Qu3d45/Dissertacao_final/Apendice/Diagrama_Blocos.png

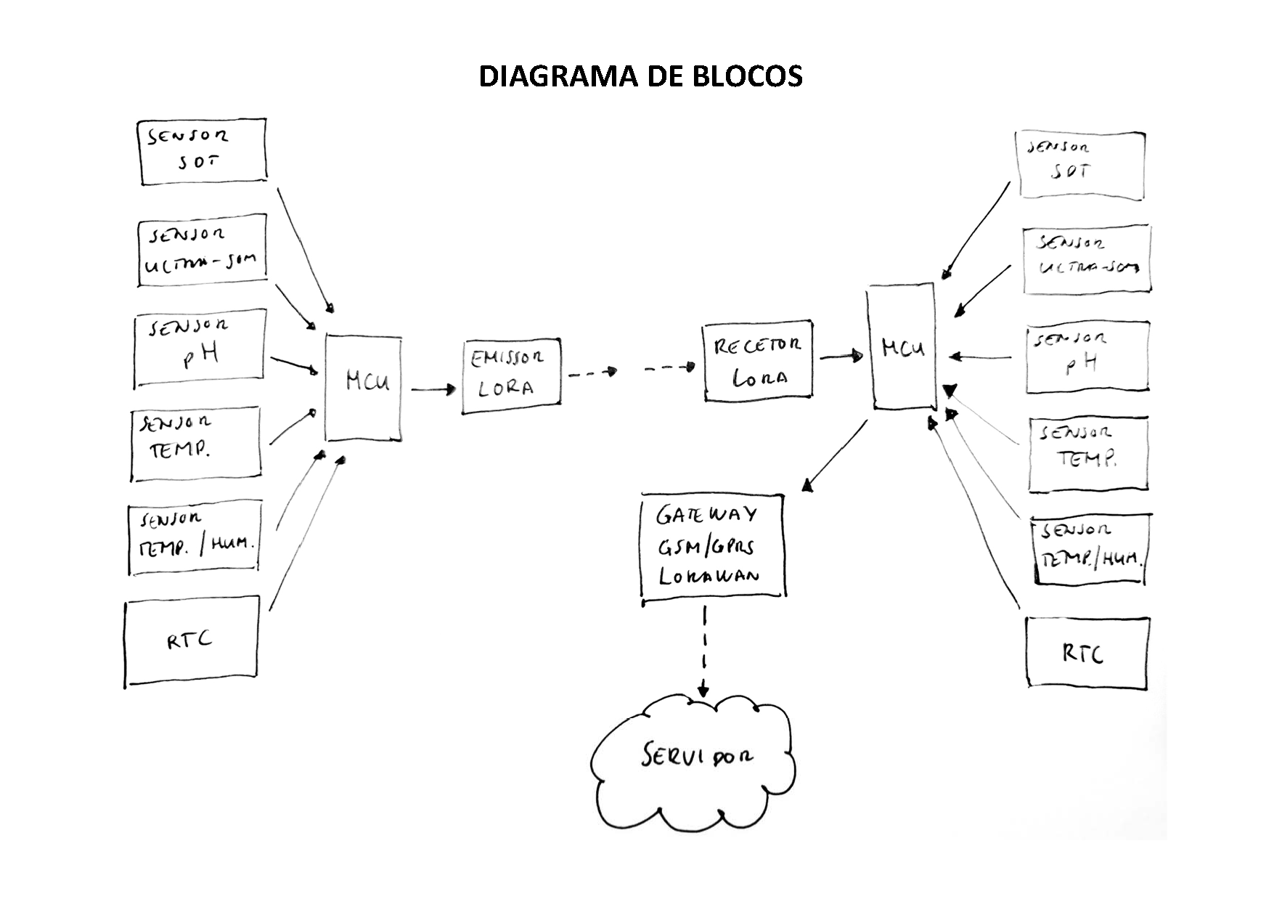
Apendice/Diagrama_Blocos.png
