Qu3d45/Dissertacao_final/Imagens_diagramas/20191011_103415.jpg

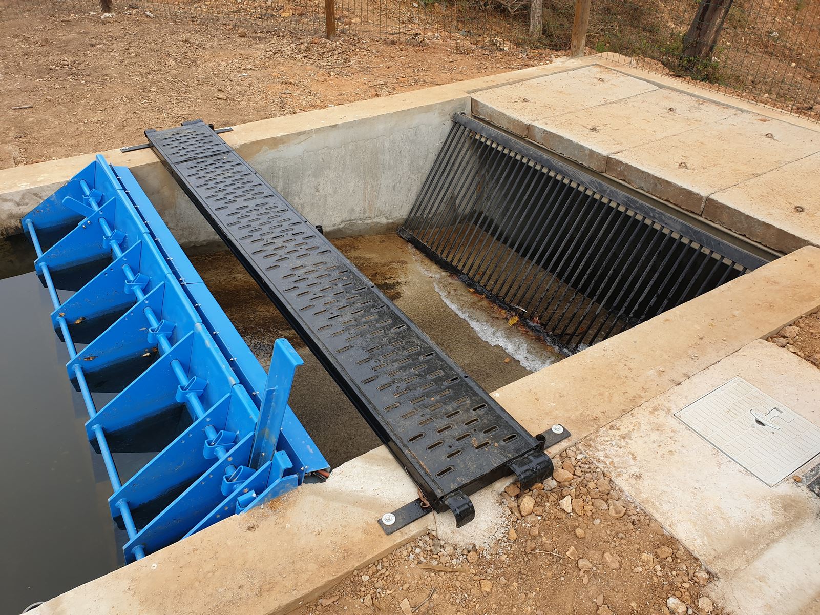
Imagens_diagramas/20191011_103415.jpg
