Qu3d45/Dissertacao_final/Imagens_diagramas/bat_liga.png

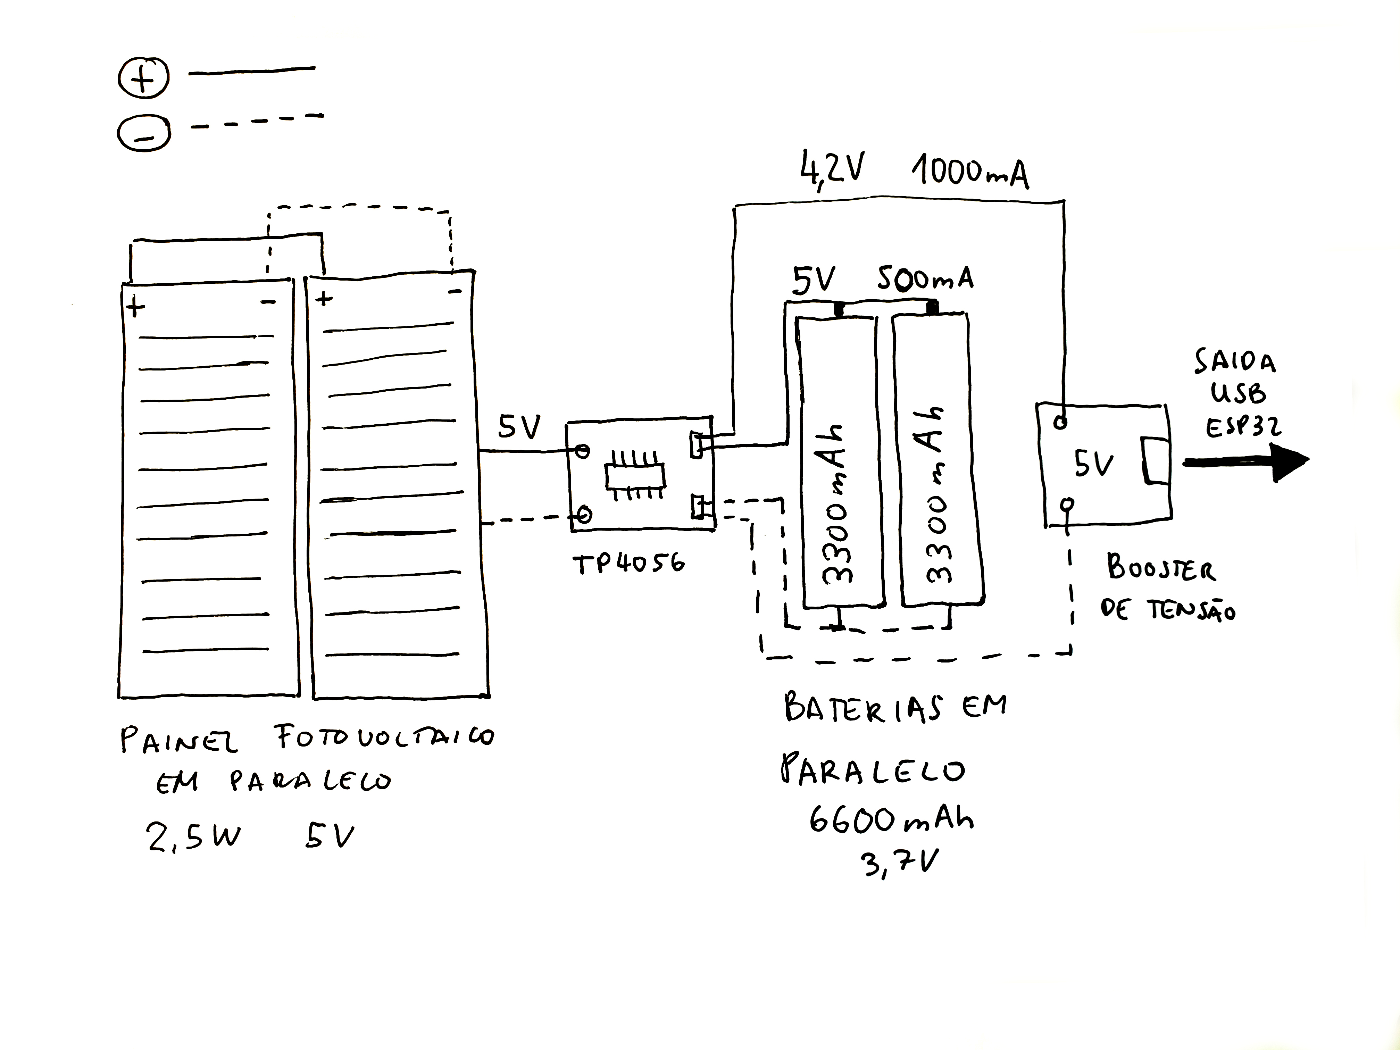
Imagens_diagramas/bat_liga.png
