Qu3d45/Dissertacao_final/Imagens_diagramas/bat_super.png

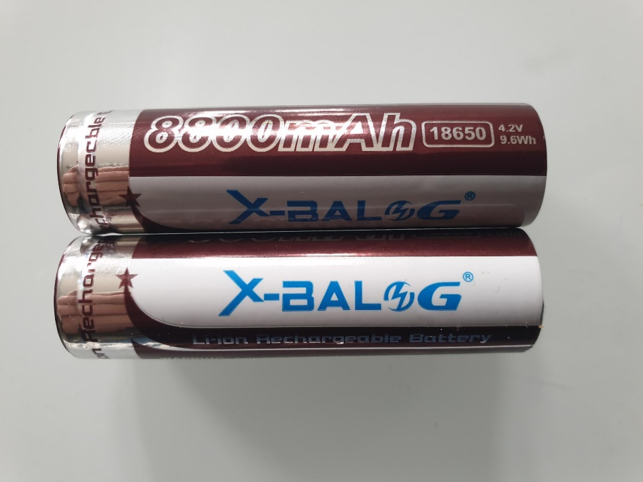
Imagens_diagramas/bat_super.png
