Qu3d45/Dissertacao_final/Imagens_diagramas/bateria.png

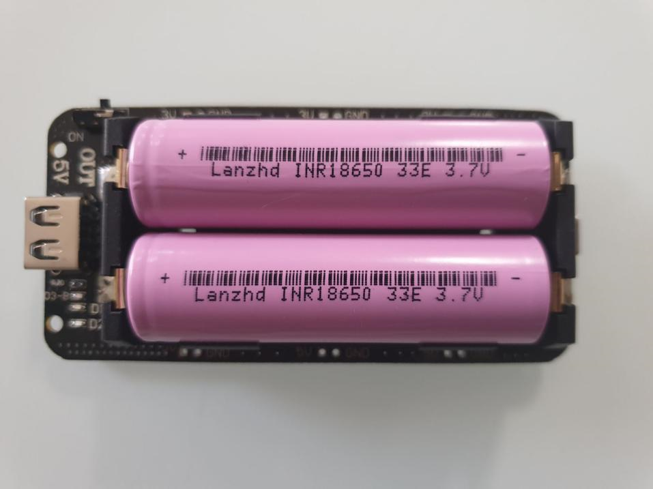
Imagens_diagramas/bateria.png
