Qu3d45/Dissertacao_final/Imagens_diagramas/bloco_emissor.png

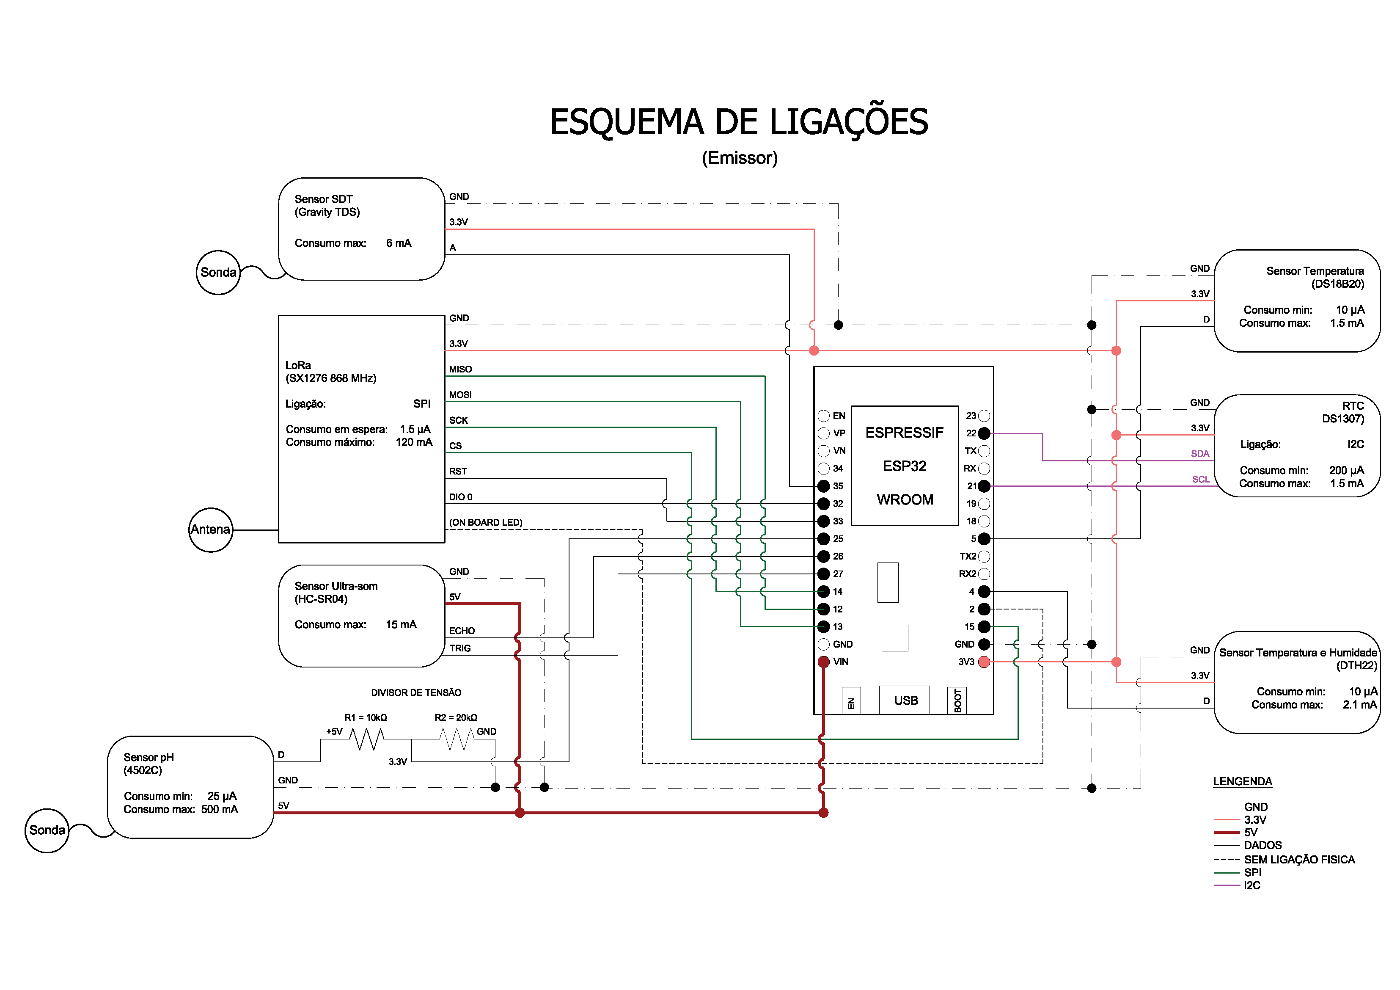
Imagens_diagramas/bloco_emissor.png
