Qu3d45/Dissertacao_final/Imagens_diagramas/bloco_gateway.png

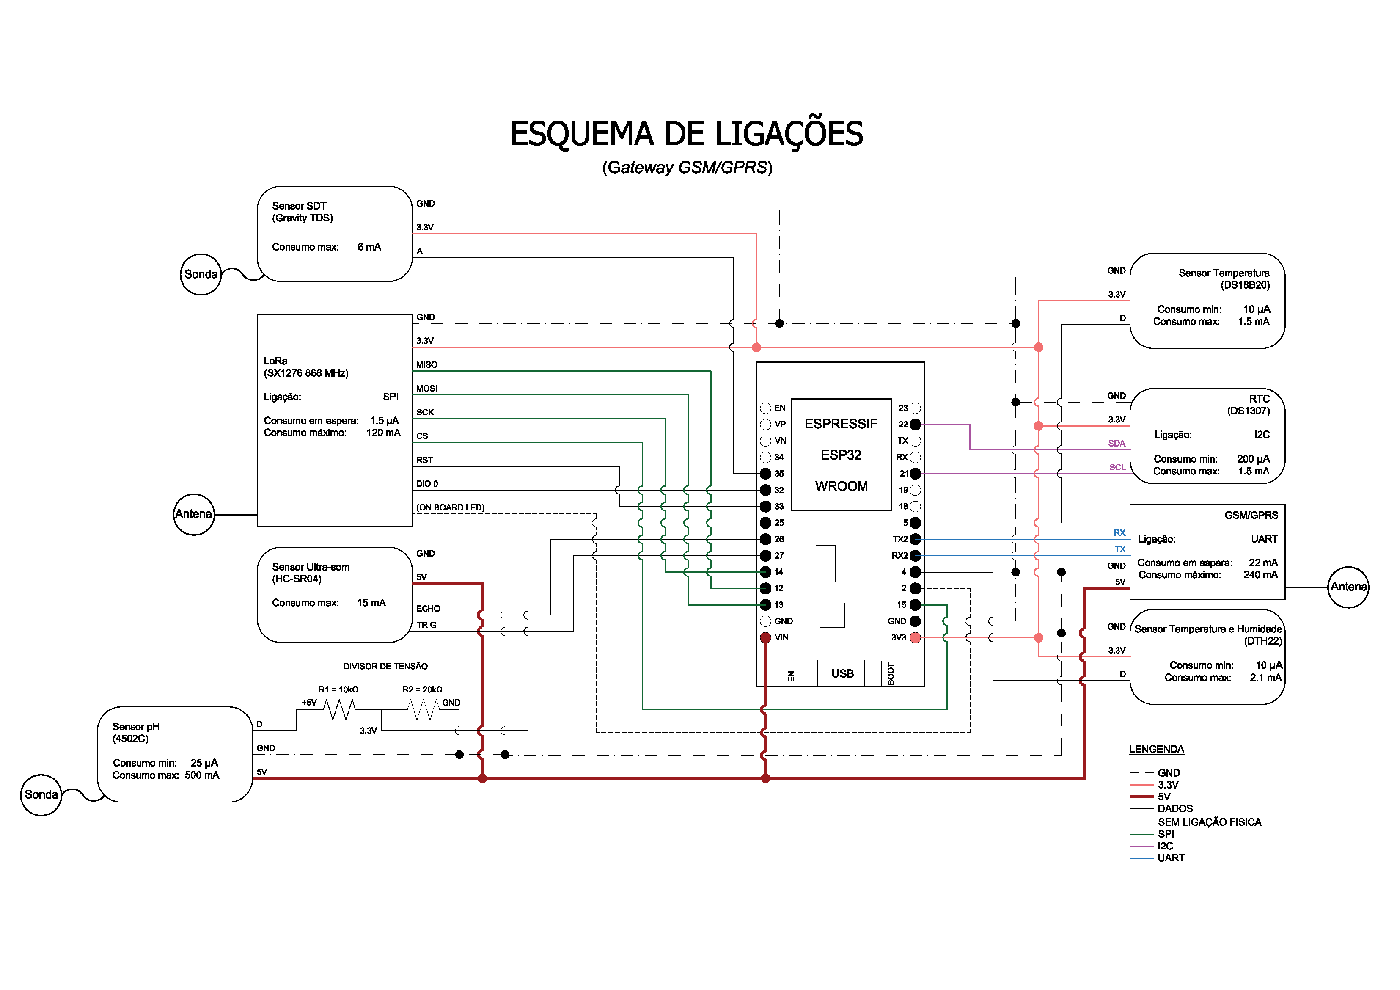
Imagens_diagramas/bloco_gateway.png
