Qu3d45/Dissertacao_final/Imagens_diagramas/caudal_1.png

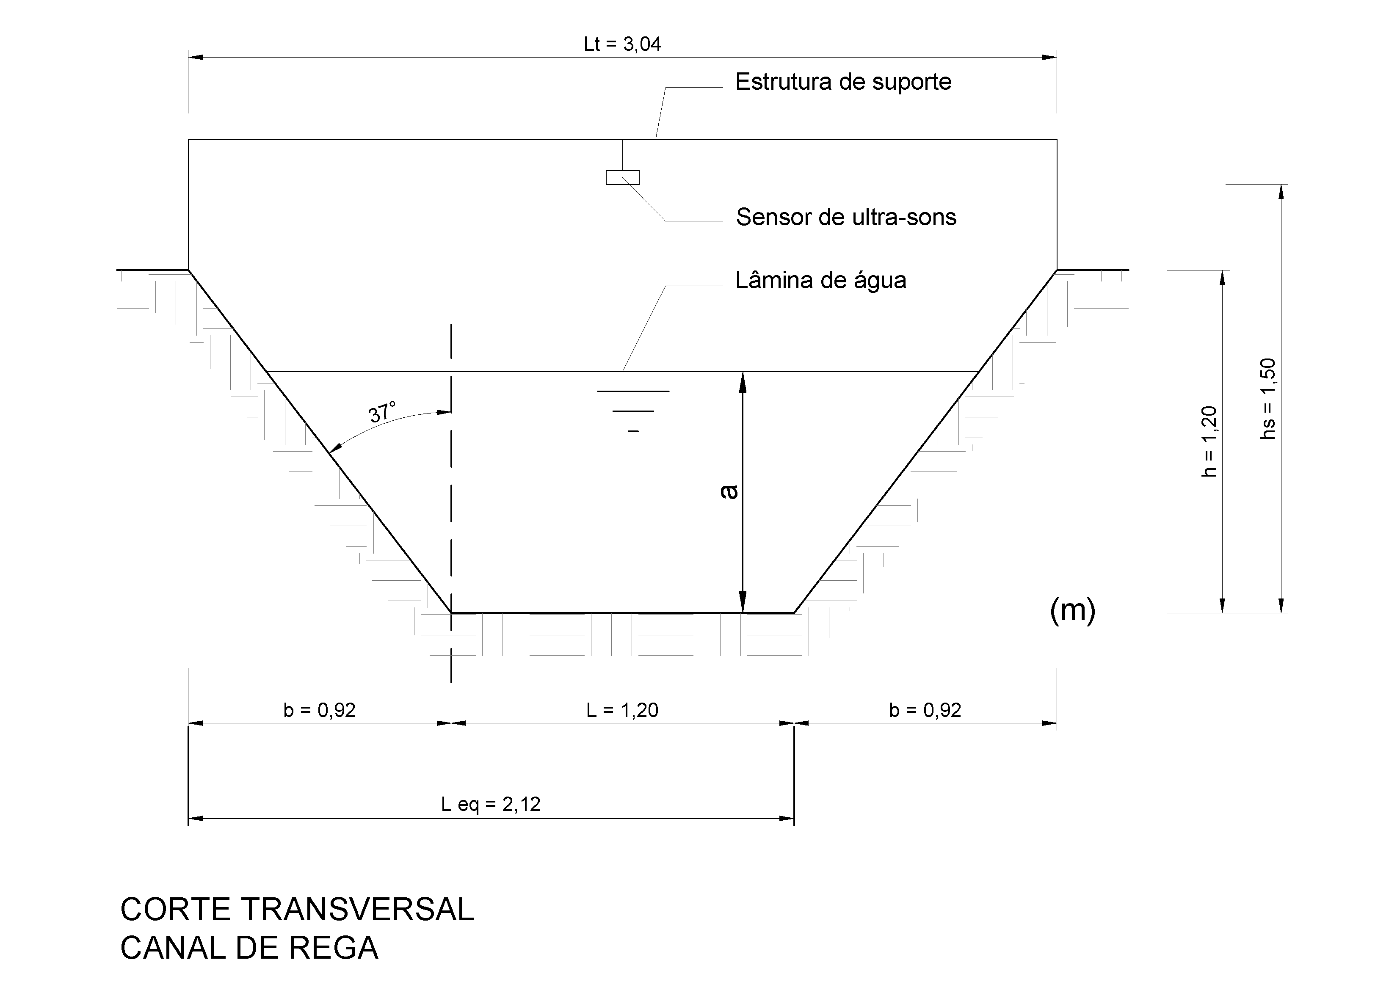
Imagens_diagramas/caudal_1.png
