Qu3d45/Dissertacao_final/Imagens_diagramas/caudal_2.png

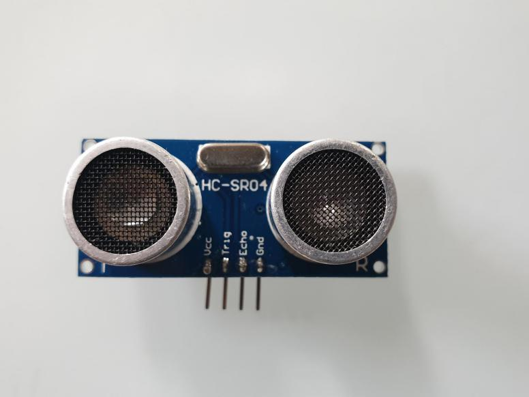
Imagens_diagramas/caudal_2.png
