Qu3d45/Dissertacao_final/Imagens_diagramas/caudal_ultrasom.png

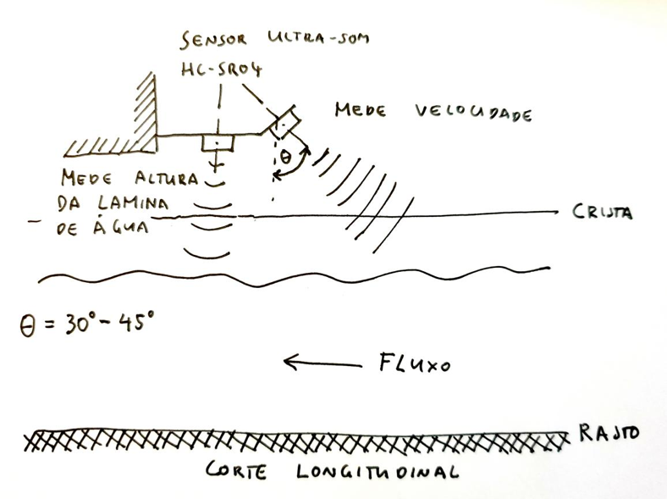
Imagens_diagramas/caudal_ultrasom.png
