Qu3d45/Dissertacao_final/Imagens_diagramas/ds18_parasita.png

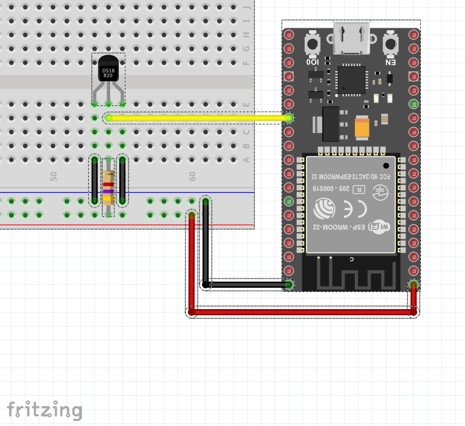
Imagens_diagramas/ds18_parasita.png
