Qu3d45/Dissertacao_final/Imagens_diagramas/ds18_serie.png

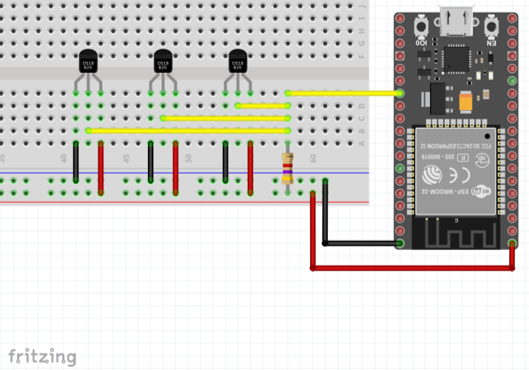
Imagens_diagramas/ds18_serie.png
