Qu3d45/Dissertacao_final/Imagens_diagramas/ds1820.png

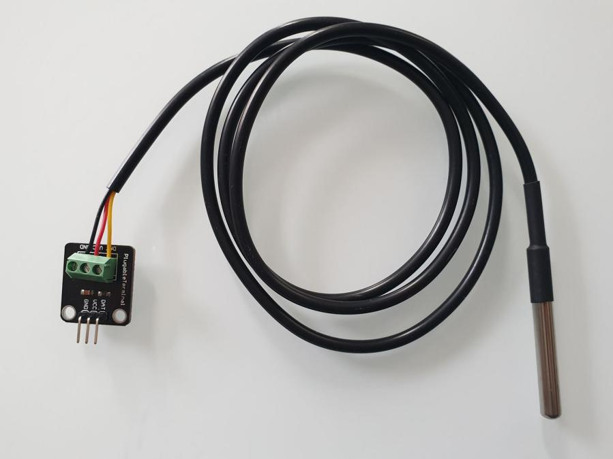
Imagens_diagramas/ds1820.png
