Qu3d45/Dissertacao_final/Imagens_diagramas/esp32.png

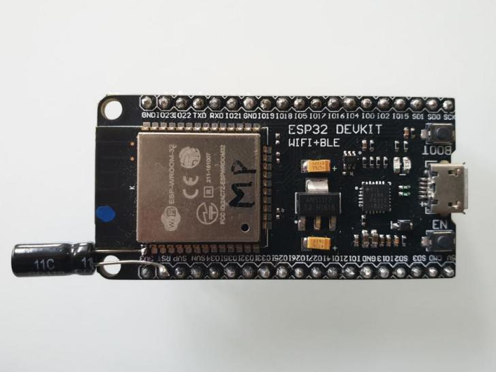
Imagens_diagramas/esp32.png
