Qu3d45/Dissertacao_final/Imagens_diagramas/esp_lora.png

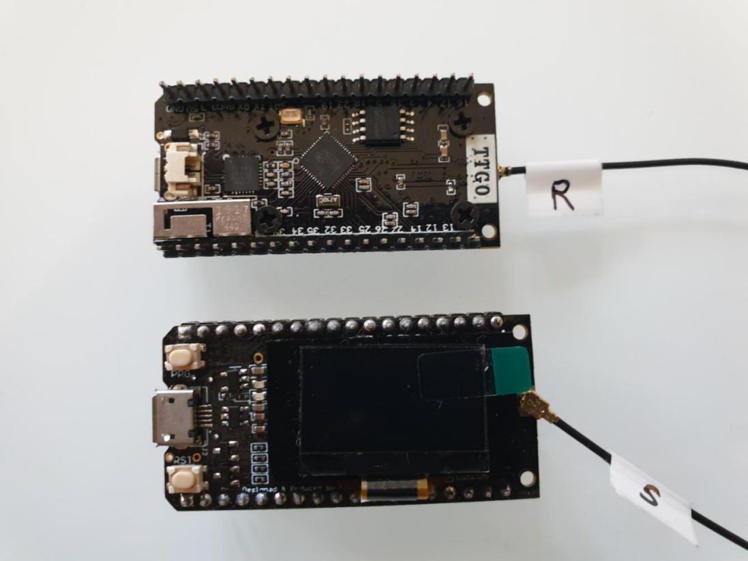
Imagens_diagramas/esp_lora.png
