Qu3d45/Dissertacao_final/Imagens_diagramas/globalagua.png

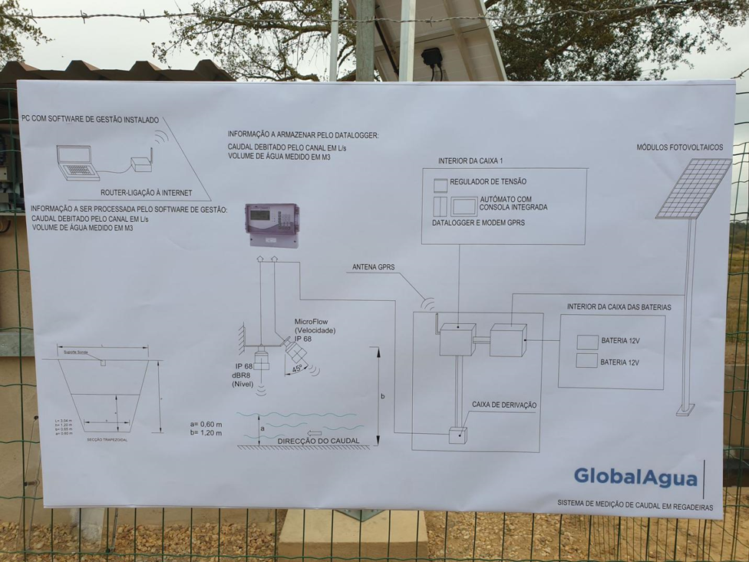
Imagens_diagramas/globalagua.png
