Qu3d45/Dissertacao_final/Imagens_diagramas/mapa_arbcas.png

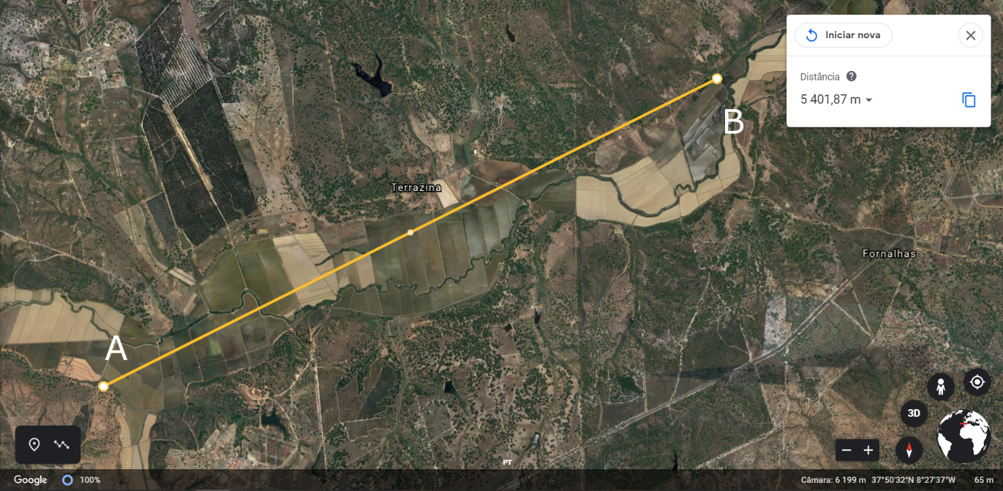
Imagens_diagramas/mapa_arbcas.png
