Qu3d45/Dissertacao_final/Imagens_diagramas/modulo_lora.png

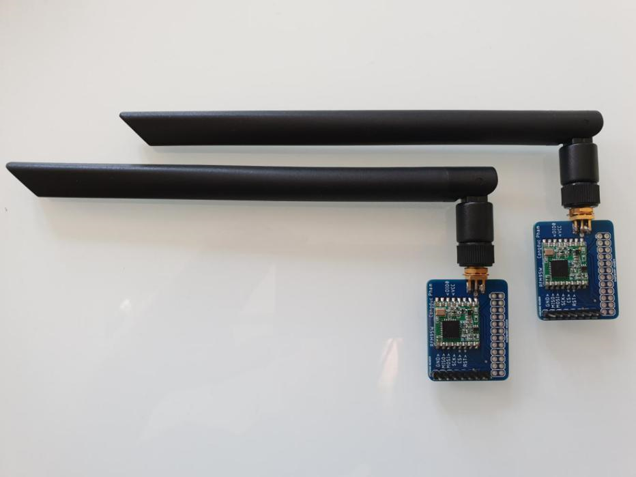
Imagens_diagramas/modulo_lora.png
