Qu3d45/Dissertacao_final/Imagens_diagramas/molinete.png

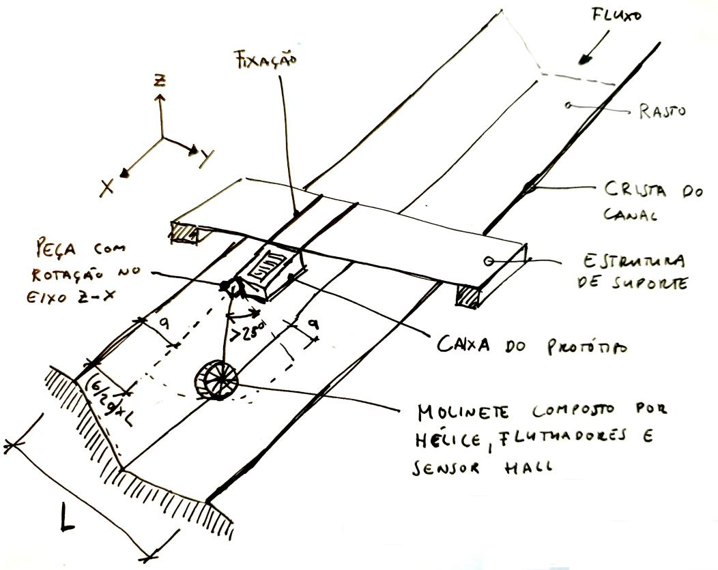
Imagens_diagramas/molinete.png
