Qu3d45/Dissertacao_final/Imagens_diagramas/nitrato.png

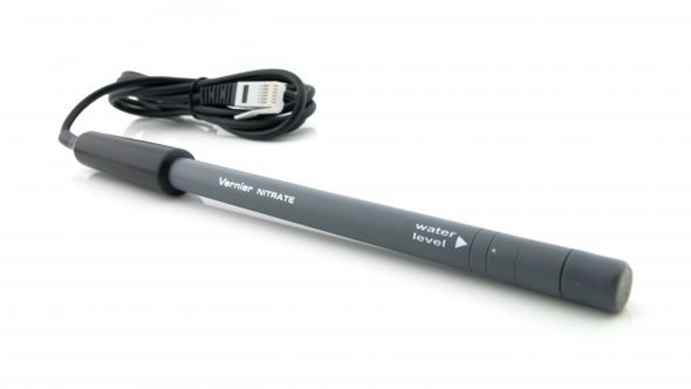
Imagens_diagramas/nitrato.png
