Qu3d45/Dissertacao_final/Imagens_diagramas/nogsm.png

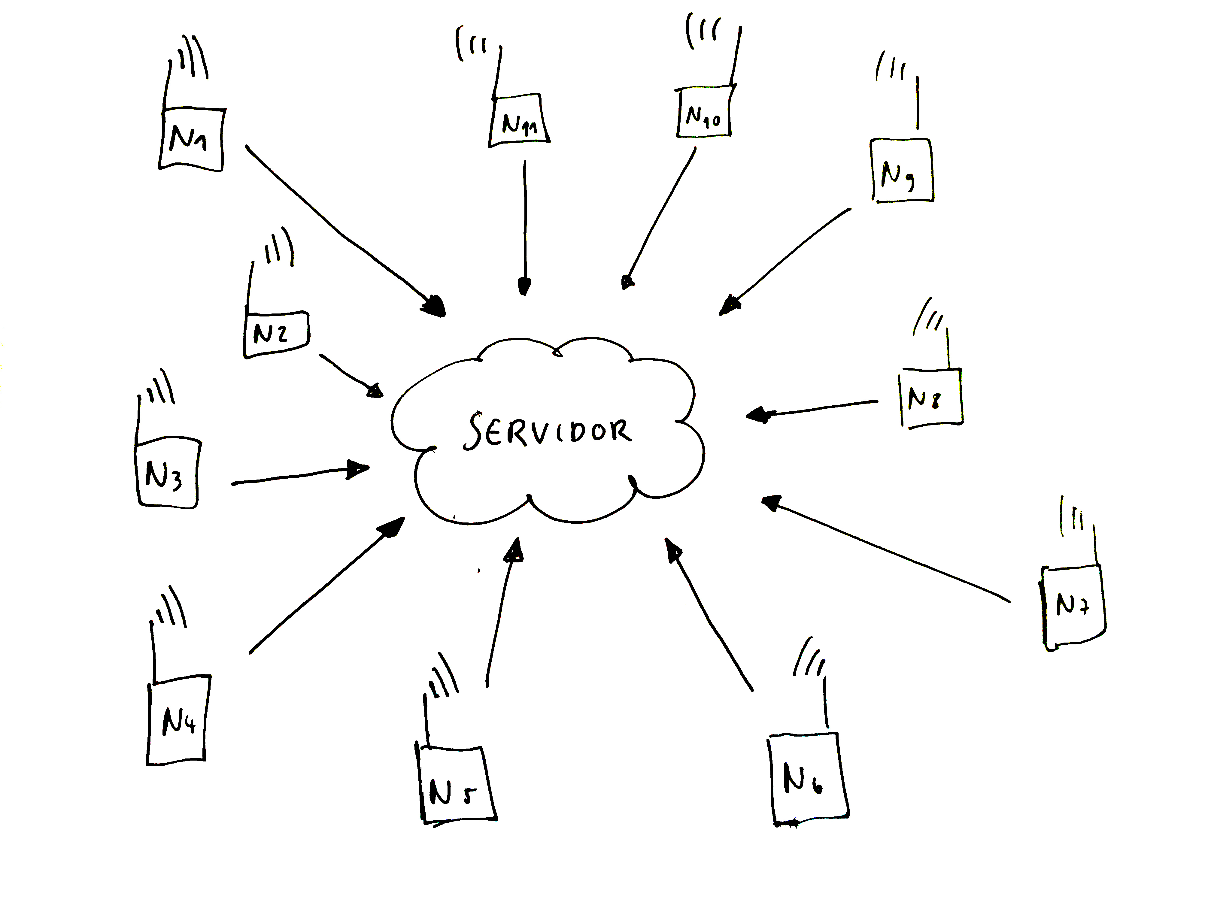
Imagens_diagramas/nogsm.png
