Qu3d45/Dissertacao_final/Imagens_diagramas/noloragsm.png

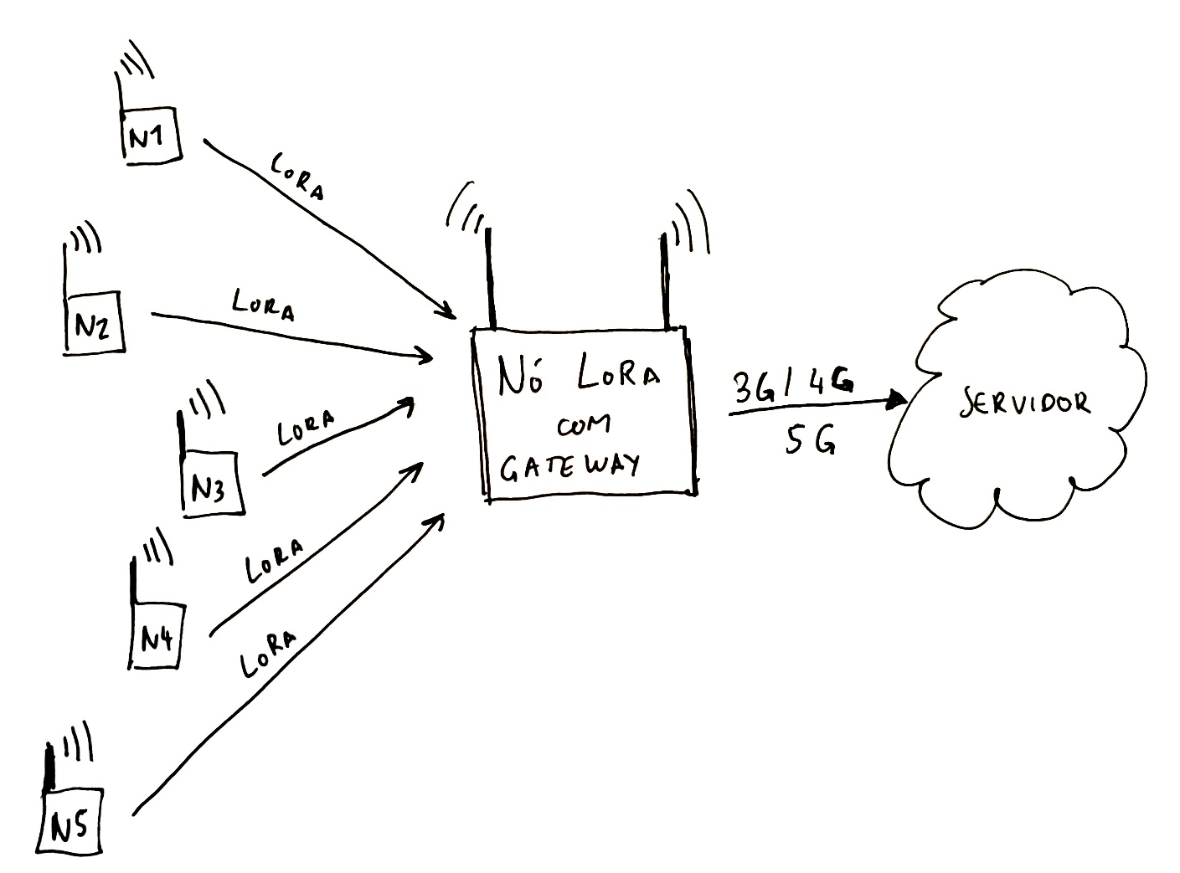
Imagens_diagramas/noloragsm.png
