Qu3d45/Dissertacao_final/Imagens_diagramas/noloralora.png

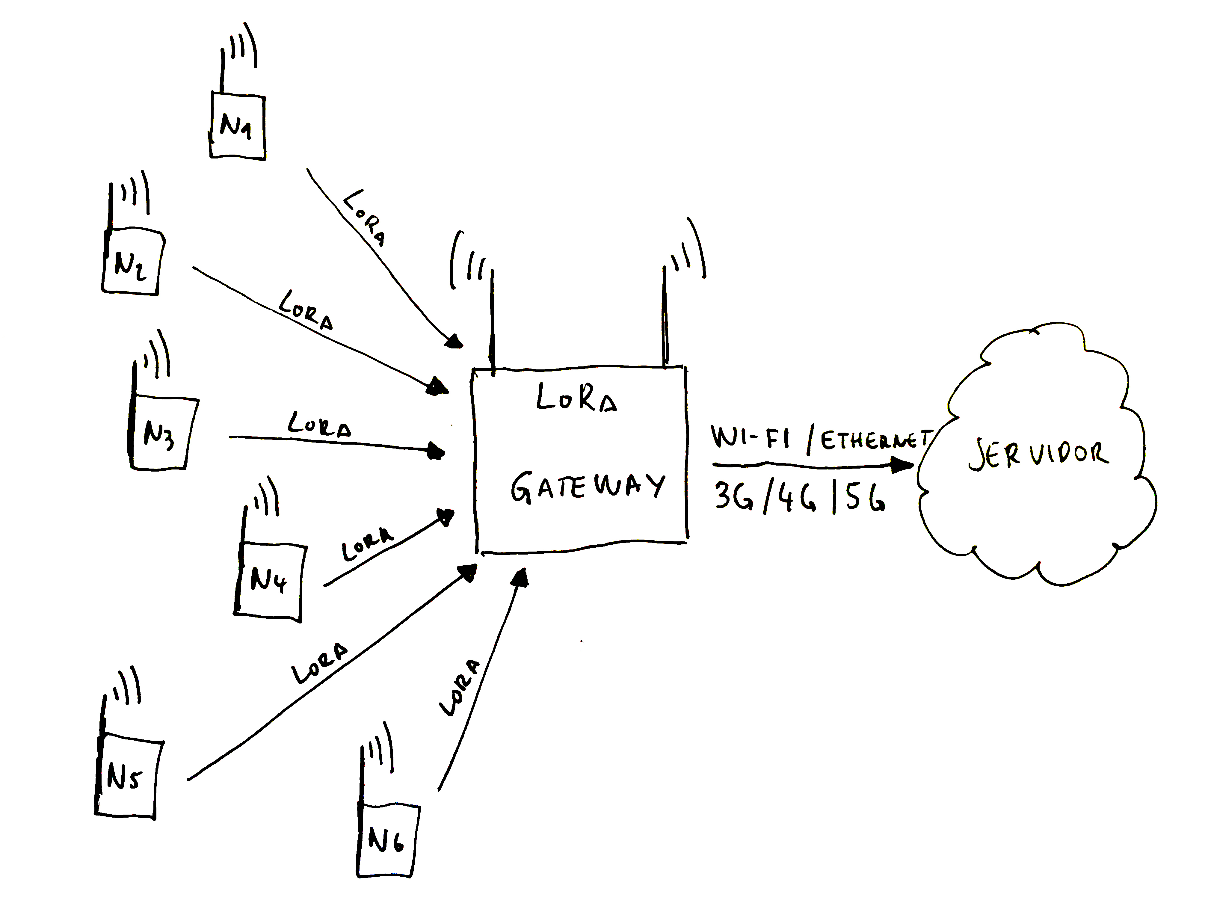
Imagens_diagramas/noloralora.png
