Qu3d45/Dissertacao_final/Imagens_diagramas/painel.png

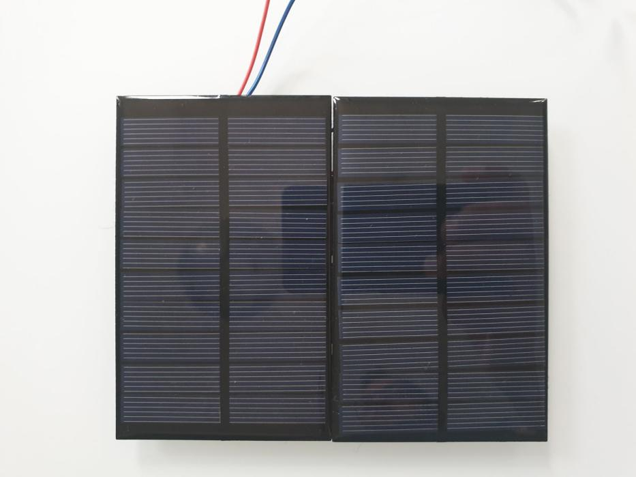
Imagens_diagramas/painel.png
