Qu3d45/Dissertacao_final/Imagens_diagramas/ph_4502_5.png

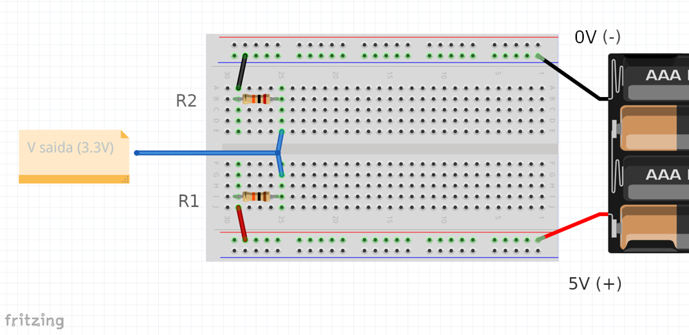
Imagens_diagramas/ph_4502_5.png
