Qu3d45/Dissertacao_final/Imagens_diagramas/pin_esp32.png

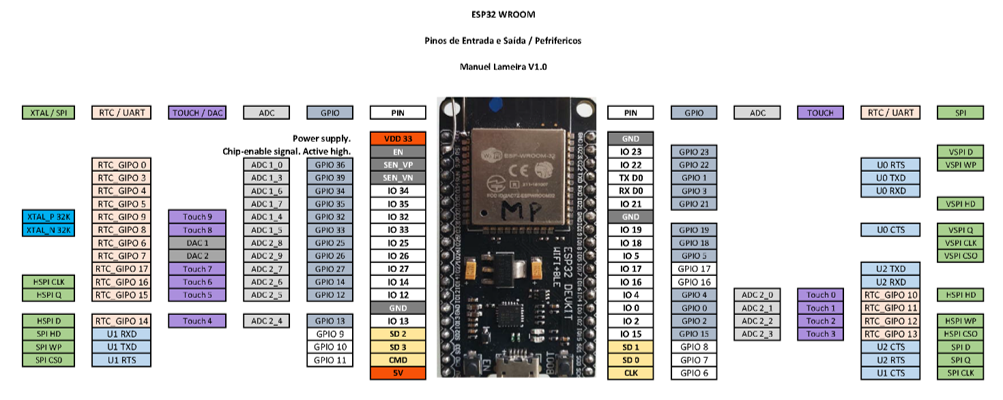
Imagens_diagramas/pin_esp32.png
