Qu3d45/Dissertacao_final/Imagens_diagramas/prototipo1.png

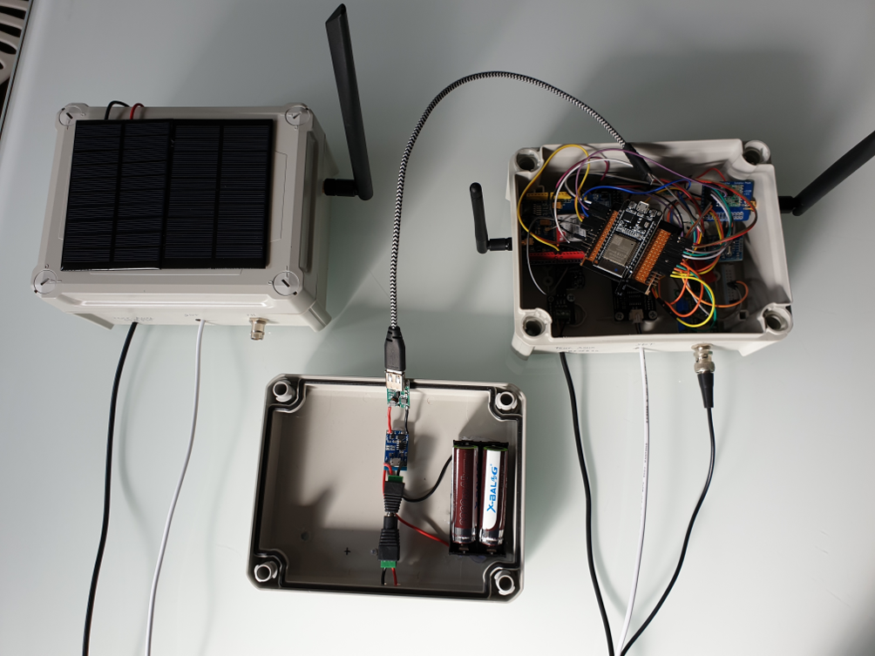
Imagens_diagramas/prototipo1.png
