Qu3d45/Dissertacao_final/Imagens_diagramas/prototipo2.png

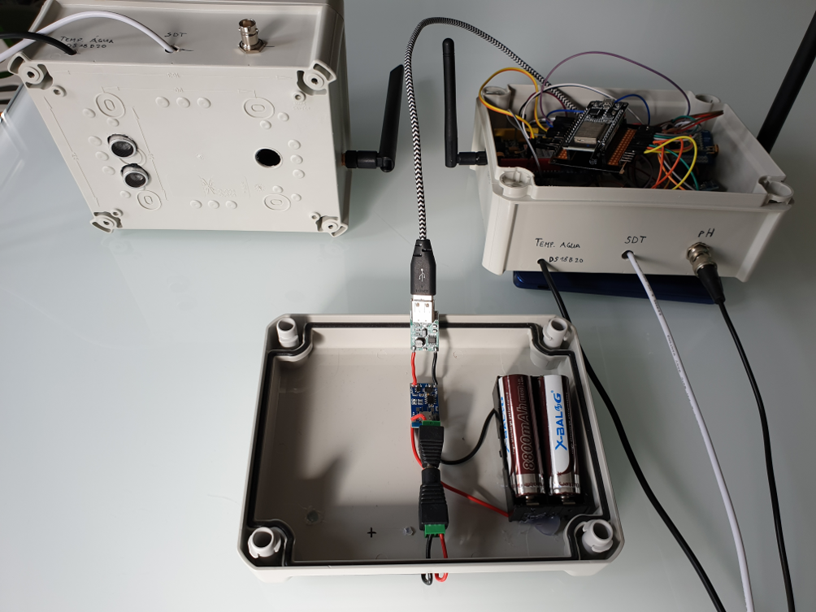
Imagens_diagramas/prototipo2.png
