Qu3d45/Dissertacao_final/Imagens_diagramas/prototipo3.png

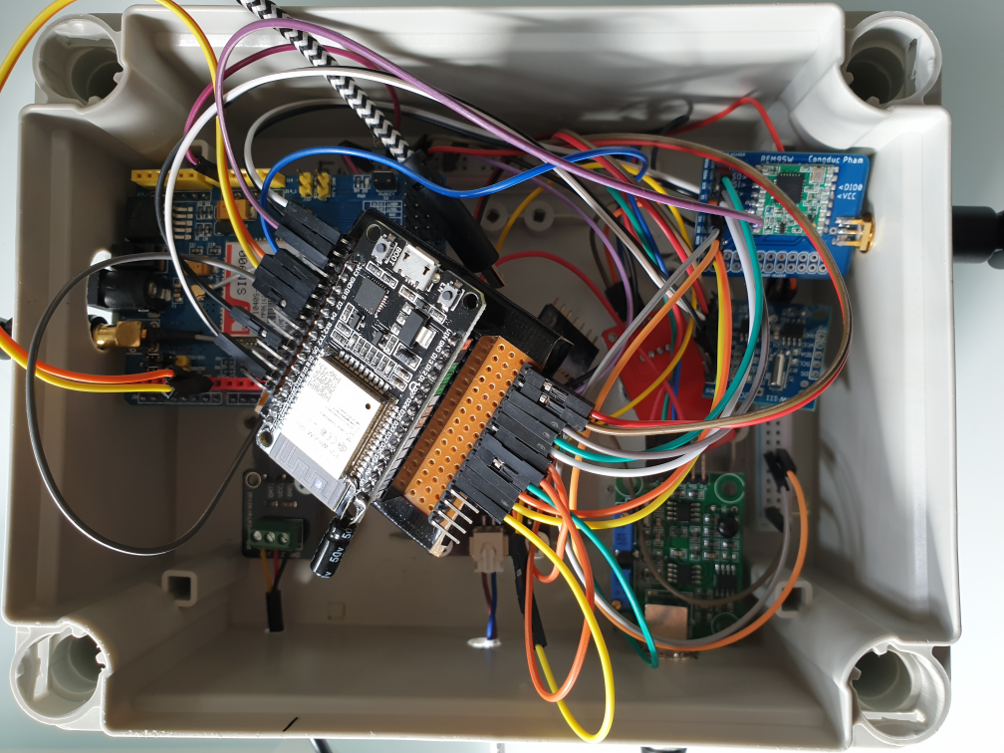
Imagens_diagramas/prototipo3.png
