Qu3d45/Dissertacao_final/Imagens_diagramas/prototipo4.png

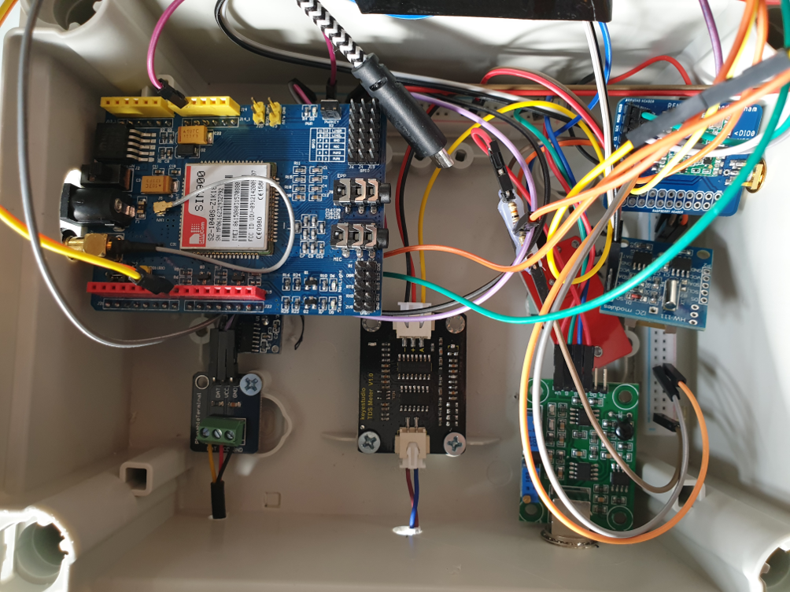
Imagens_diagramas/prototipo4.png
