Qu3d45/Dissertacao_final/Imagens_diagramas/prototipo5.png

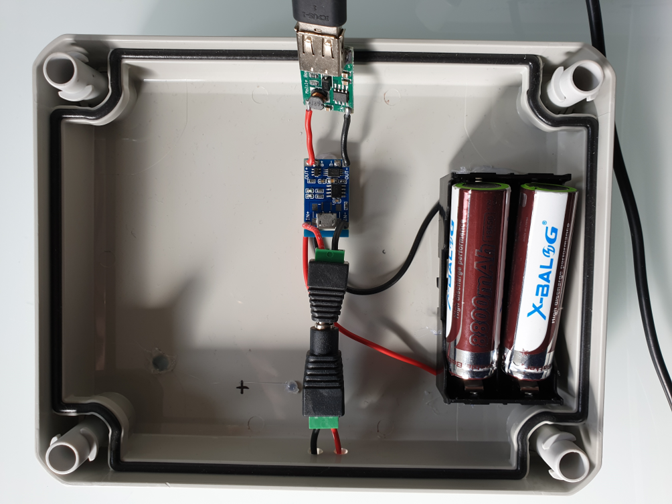
Imagens_diagramas/prototipo5.png
