Qu3d45/Dissertacao_final/Imagens_diagramas/pyboard.png

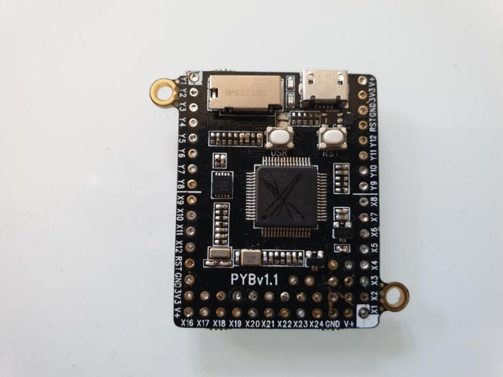
Imagens_diagramas/pyboard.png
