Qu3d45/Dissertacao_final/Imagens_diagramas/RFID1.jpg

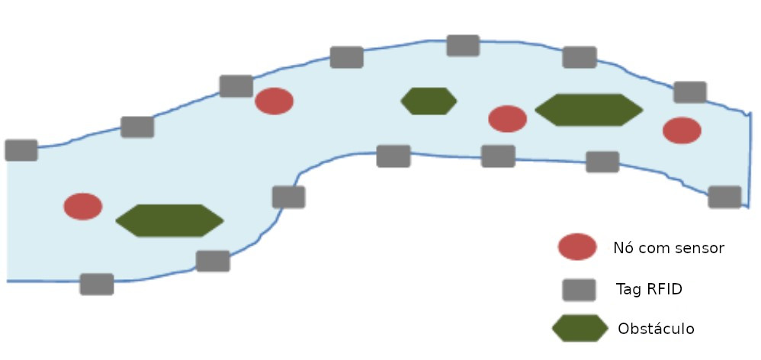
Imagens_diagramas/RFID1.jpg
