Qu3d45/Dissertacao_final/Imagens_diagramas/rtc.png

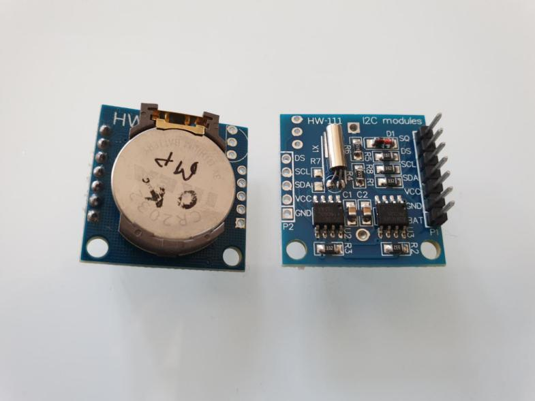
Imagens_diagramas/rtc.png
