Qu3d45/Dissertacao_final/Imagens_diagramas/sdt.png

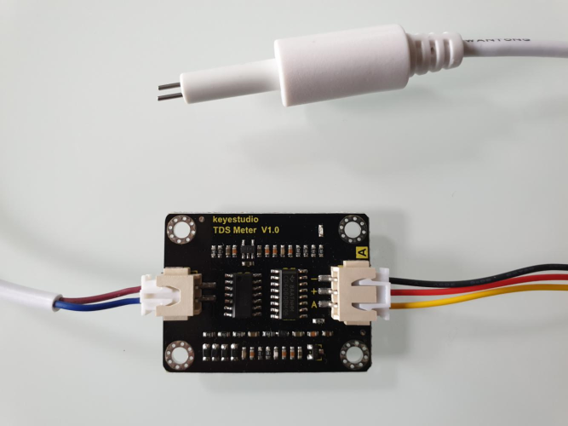
Imagens_diagramas/sdt.png
