Qu3d45/Dissertacao_final/Imagens_diagramas/sim900.png

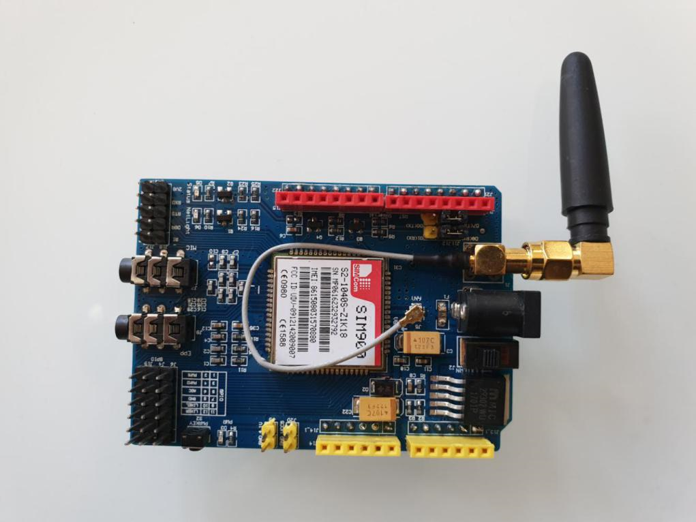
Imagens_diagramas/sim900.png
