Qu3d45/Dissertacao_final/Imagens_diagramas/tds.png

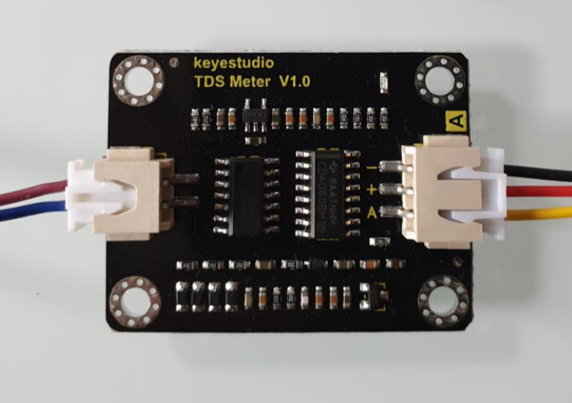
Imagens_diagramas/tds.png
