Qu3d45/Dissertacao_final/Imagens_diagramas/tp4056.png

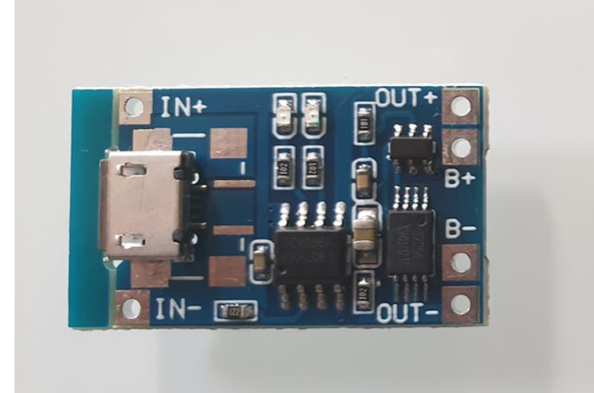
Imagens_diagramas/tp4056.png
