Qu3d45/Dissertacao_final/Imagens_diagramas/tp_booster.png

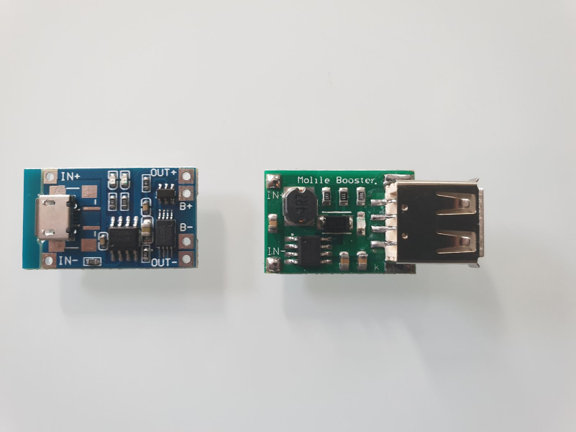
Imagens_diagramas/tp_booster.png
