Qu3d45/Dissertacao_final/Imagens_diagramas/TS_caud_inst.png

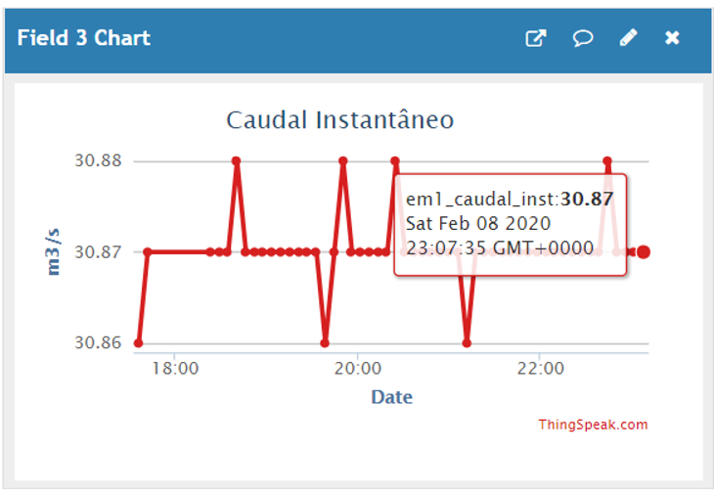
Imagens_diagramas/TS_caud_inst.png
