Qu3d45/Dissertacao_final/Imagens_diagramas/TS_hum.png

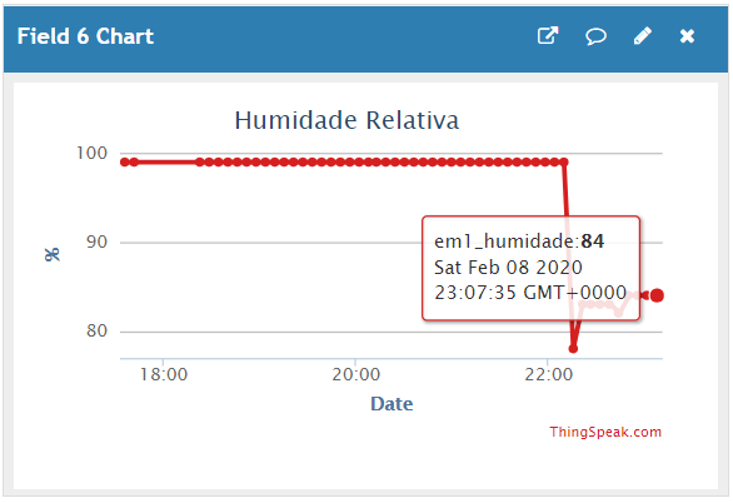
Imagens_diagramas/TS_hum.png
