Qu3d45/Dissertacao_final/Imagens_diagramas/TS_ph.png

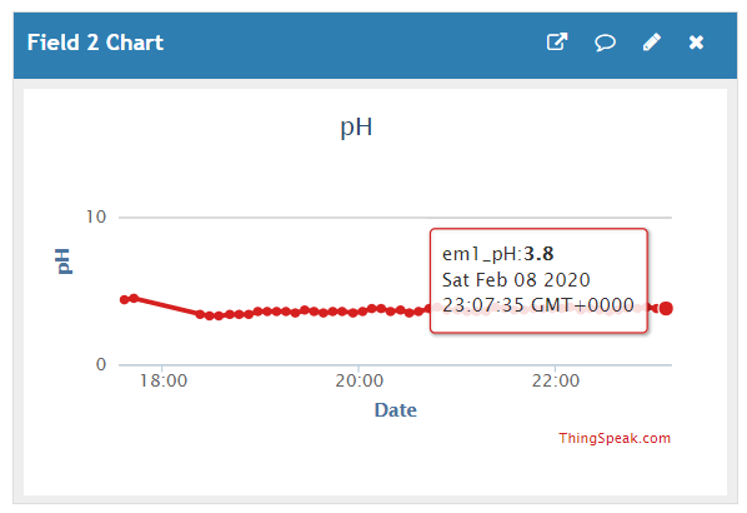
Imagens_diagramas/TS_ph.png
