Qu3d45/Dissertacao_final/Imagens_diagramas/TS_SDT.png

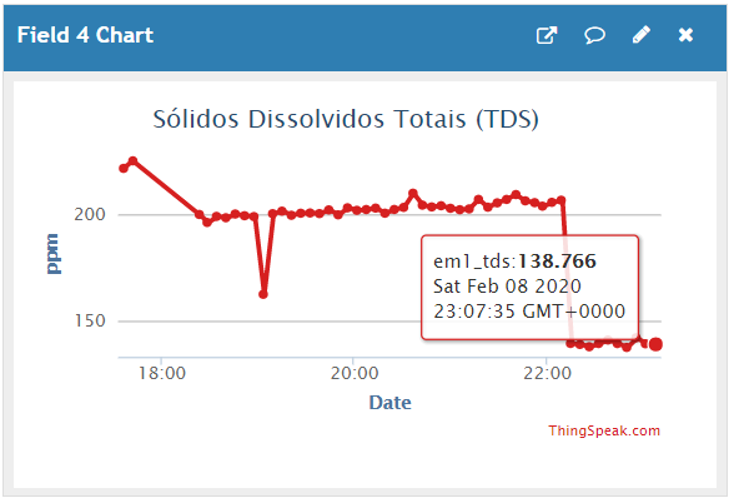
Imagens_diagramas/TS_SDT.png
