Qu3d45/Dissertacao_final/Imagens_diagramas/TS_temp_agua.png

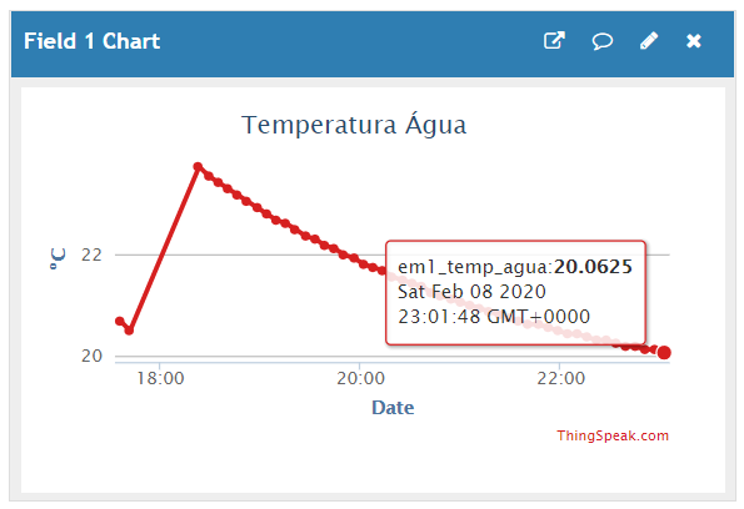
Imagens_diagramas/TS_temp_agua.png
