Qu3d45/Dissertacao_final/Imagens_diagramas/TS_temp_amb.png

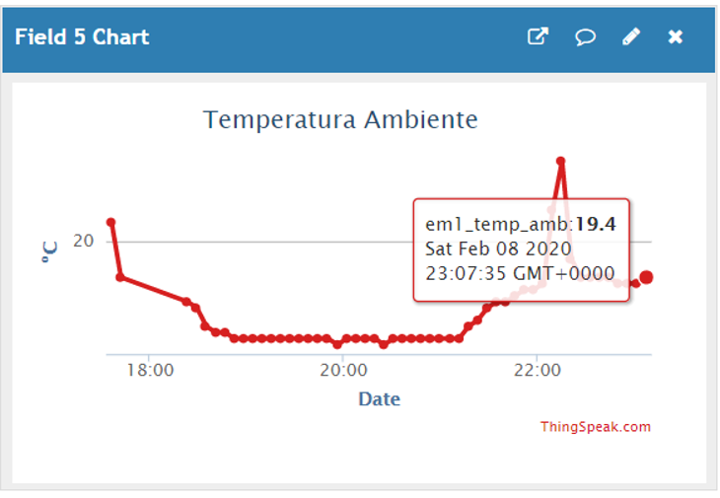
Imagens_diagramas/TS_temp_amb.png
