Qu3d45/Dissertacao_final/Imagens_diagramas/ttgo_tcell.png

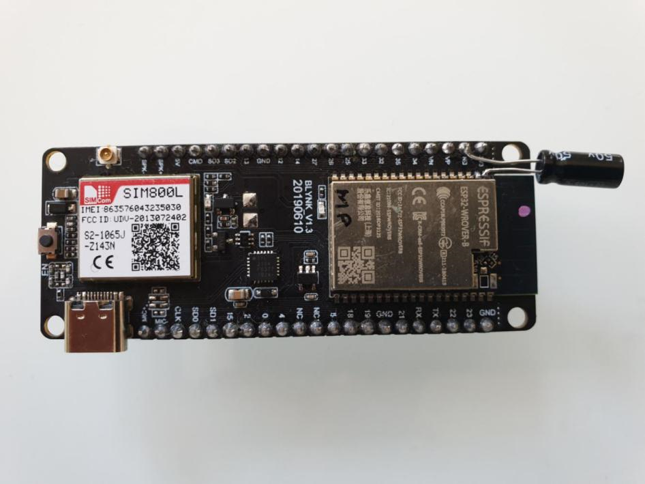
Imagens_diagramas/ttgo_tcell.png
