Qu3d45/Dissertacao_final/Apendice/Diagrama_Fluxo.pdf

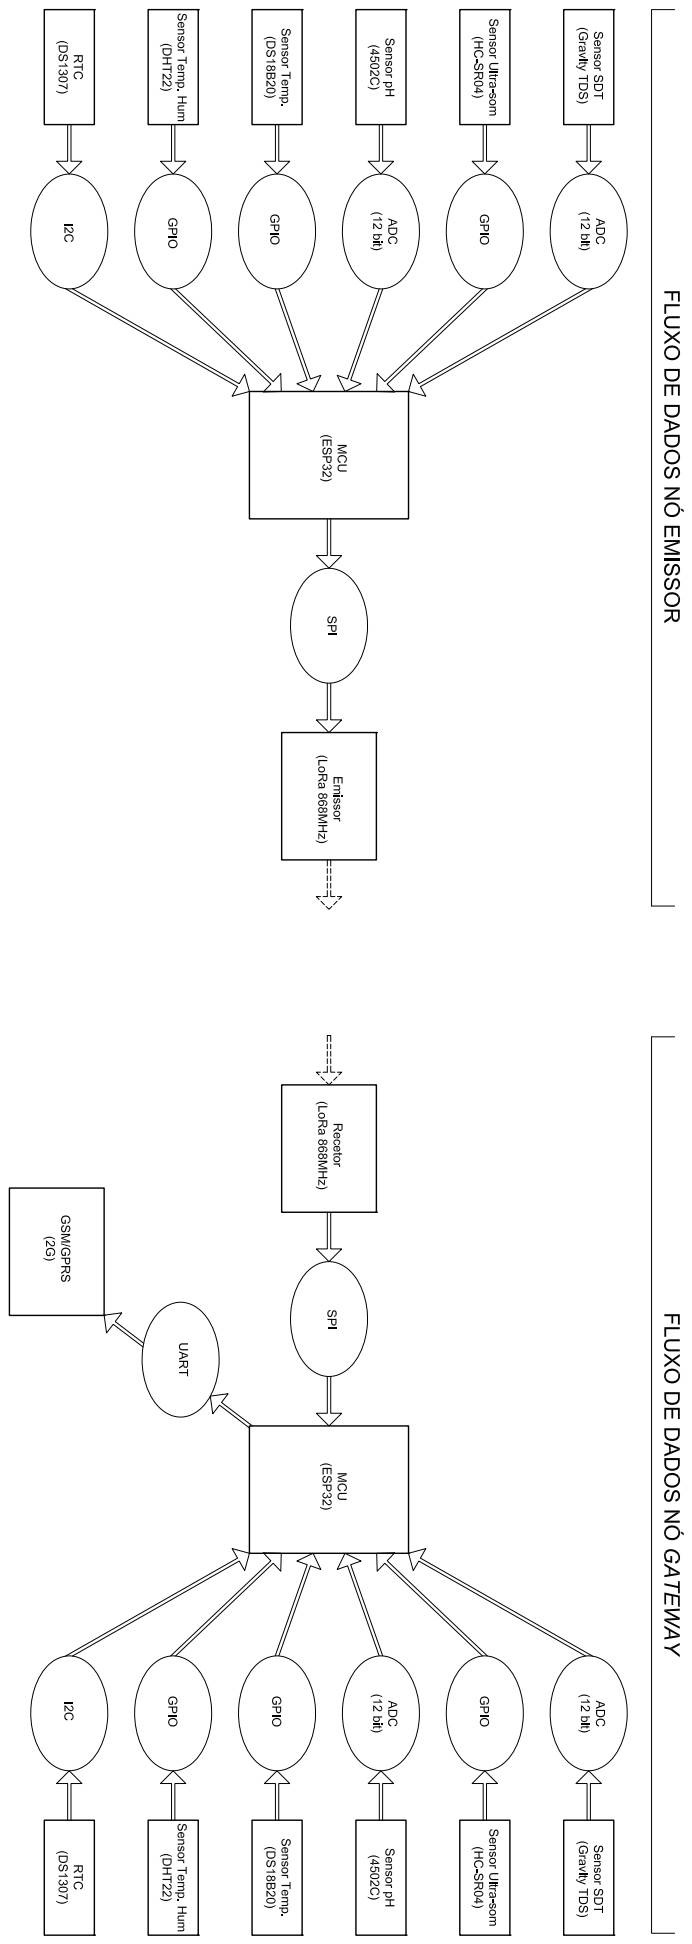
[picture p58: page 1]
