Qu3d45/Dissertacao_final/Apendice/Esquema_Ligações_Emissor.pdf

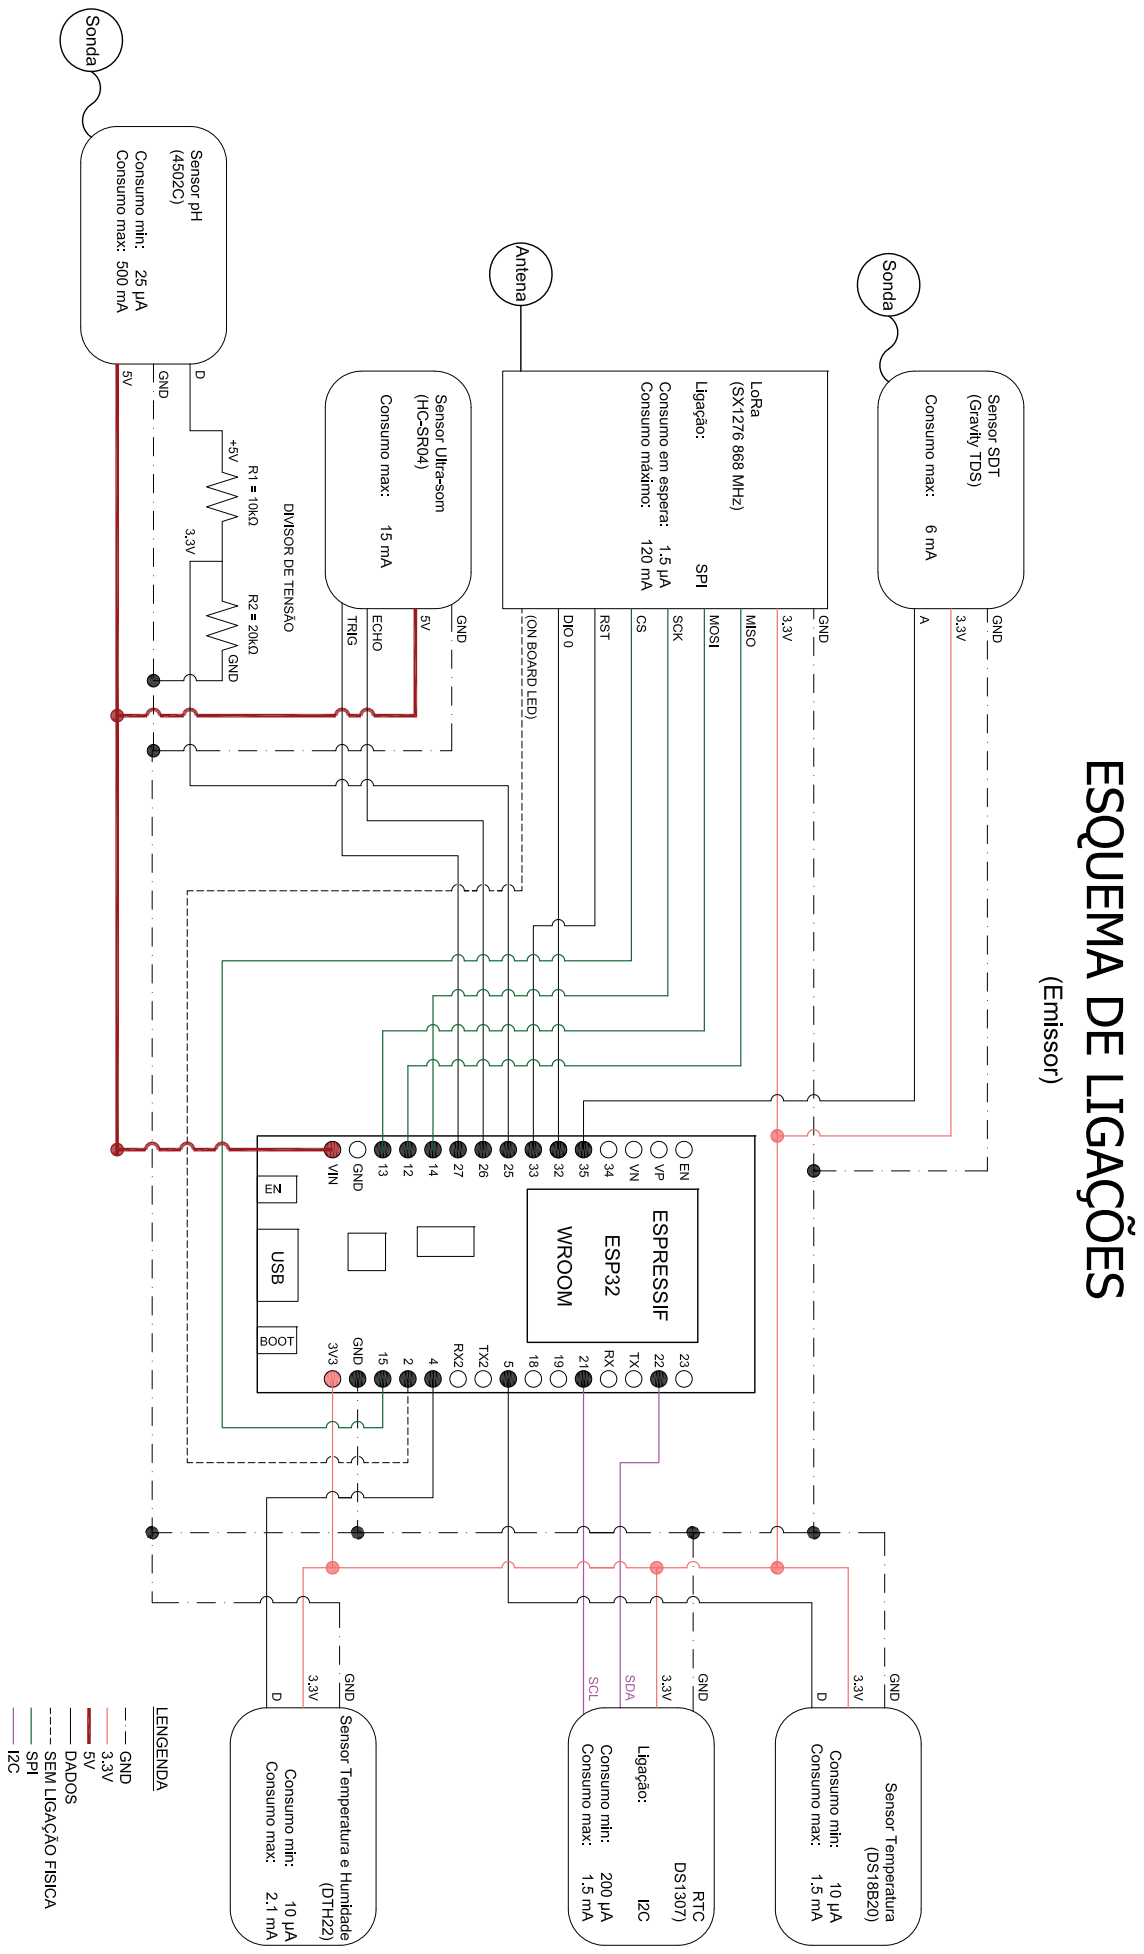
[picture p59: page 1]
