Qu3d45/Dissertacao_final/Apendice/Esquema_Ligações_Gateway.pdf

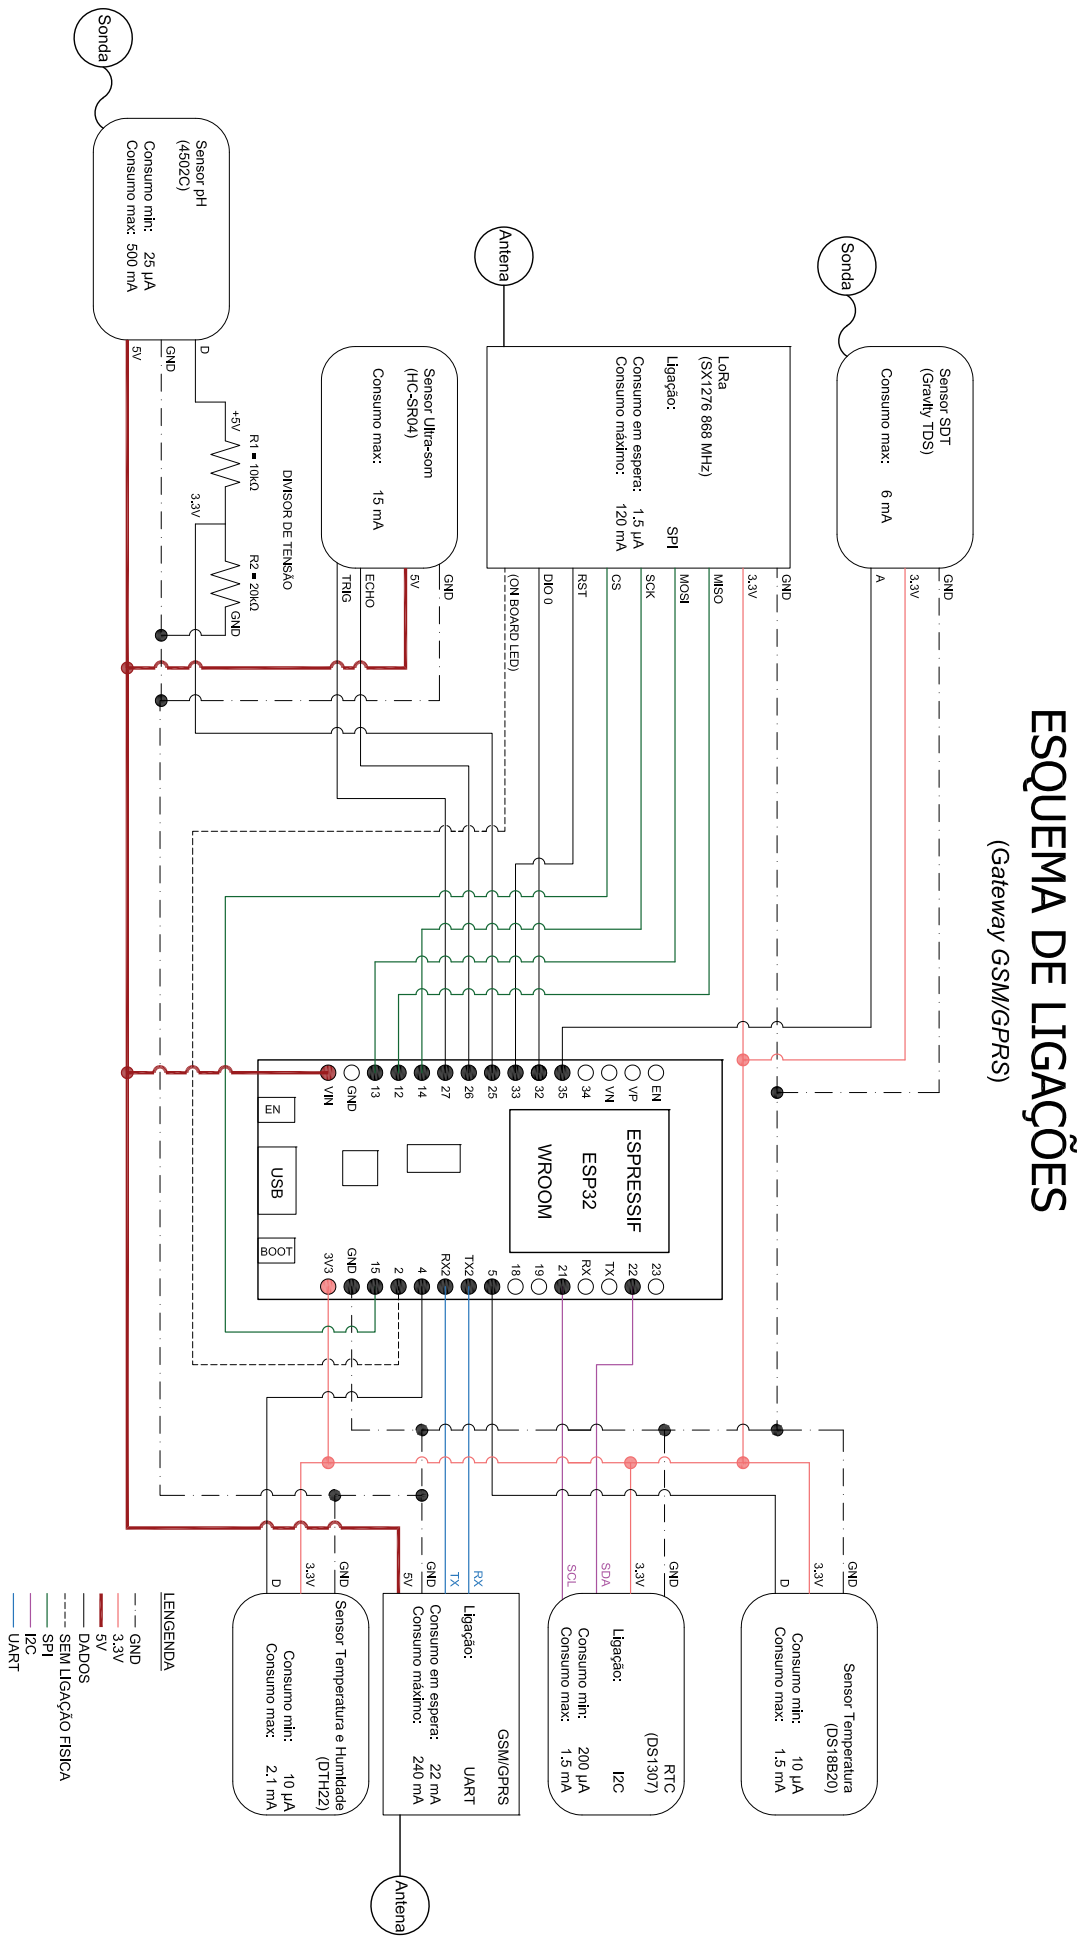
[picture p60: page 1]
